developerISP/MRGLoRaNetwork/meteorology/outputs/MRGwinddirectiontypicalyear_autunno.png

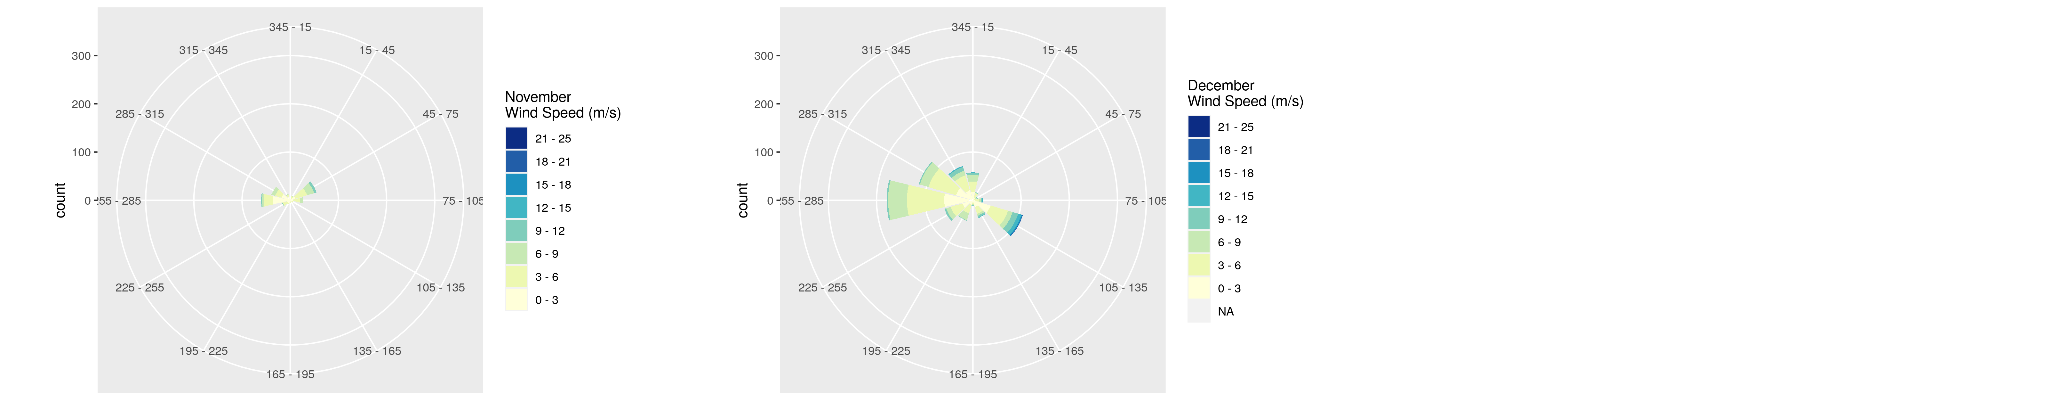
meteorology/outputs/MRGwinddirectiontypicalyear_autunno.png
