developerISP/MRGLoRaNetwork/meteorology/outputs/MRGwinddirectiontypicalyear_estate.png

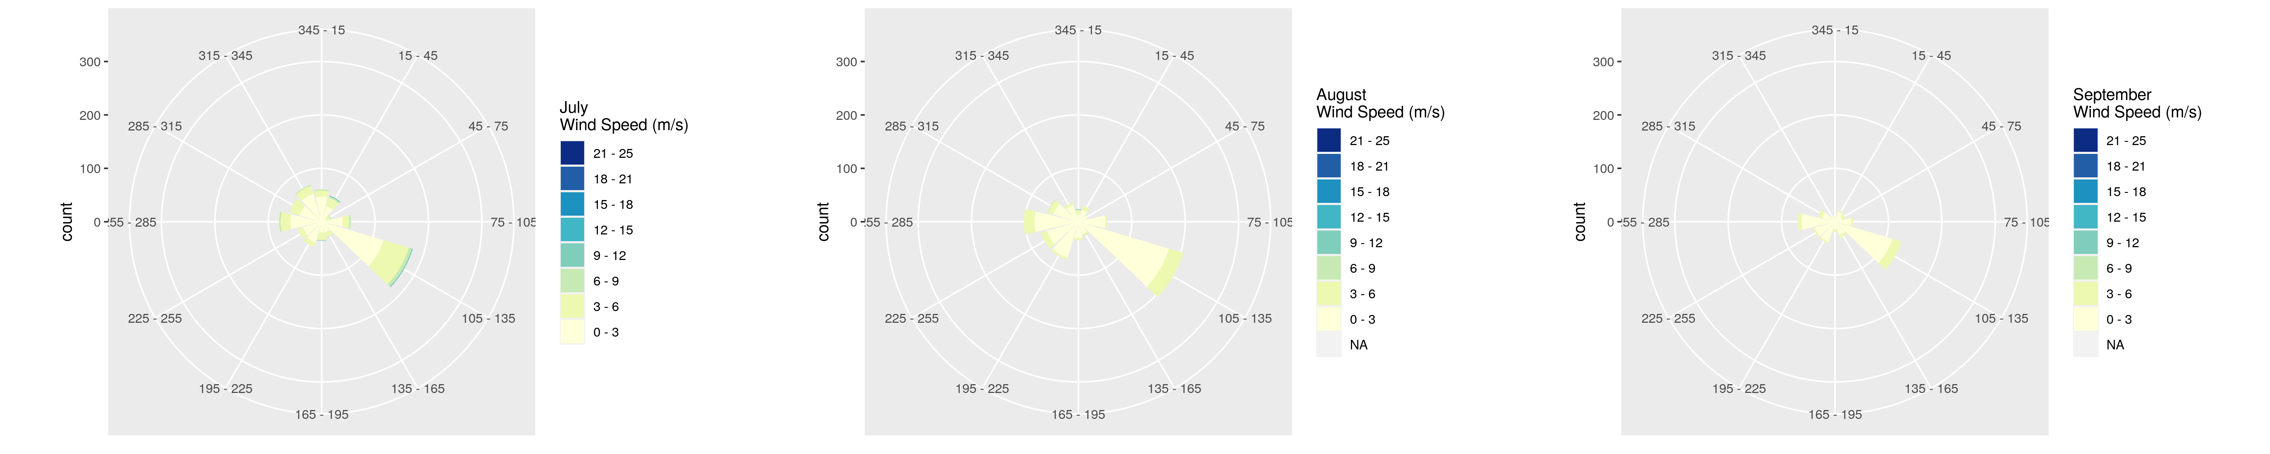
meteorology/outputs/MRGwinddirectiontypicalyear_estate.png
