developerISP/MRGLoRaNetwork/backend/pyserial/serial_read.py

#!/usr/bin/env python
import time
import serial

ser = serial.Serial(
        port='/dev/ttyS0',
        baudrate = 9600,
        parity=serial.PARITY_NONE,
        stopbits=serial.STOPBITS_ONE,
        bytesize=serial.EIGHTBITS,
        timeout=1
)

while 1:
        x=ser.readline()
        print(x)
