developerISP/MRGLoRaNetwork/ROSY-Endnode/ROSY_Utility.h

#pragma once
#ifndef _ROSY_UTILITY_H_
#define _ROSY_UTILITY_H_

namespace ROSY 
{
	namespace Utility
	{
		class Statistics;
		class Compressor;
		void sendDecompressedPacket(uint8_t packet[]);
	}
}
#endif
